cziter15/raesp_gateway/firmware/src/apps/raesp/comps/RadioCommander.cpp

/*
 *	Copyright (c) 2021-2023, Krzysztof Strehlau
 *
 *	This file is part of the RaespDevice (WiFi 433 MHz bridge) firmware.
 *	All licensing information can be found inside LICENSE.md file.
 *
 *	https://github.com/cziter15/raesp_gateway/blob/main/firmware/LICENSE
 */

#include "RadioCommander.h"
#include <RadioLib.h>

#include "board.h"
#include "../protocols/nexa.h"
#include "../protocols/ningbo.h"

using namespace std::placeholders;

namespace apps::raesp::comps
{
	RadioCommander::RadioCommander(uint8_t ssPin, uint8_t dio0pin, uint8_t rstPin, uint8_t dio2pin, ksLedWP& wifiLedWp, ksLedWP& radioLedWp)
		: radioLedWp(radioLedWp), wifiLedWp(wifiLedWp), rfTopicPrefix(PSTR("rfswitch/"))
	{
		/* Instantiate radio PHY/Module. */
		radioPhy = std::make_unique<Module>(ssPin, dio0pin, rstPin, dio2pin);
		radioModule = std::make_unique<SX1278>(radioPhy.get());

		/* Setup radio module. */
		cachedFrequency = TRANSMIT_FREQ_NEXA;
		radioModule->beginFSK(cachedFrequency, 4.8F, 5.0F, 125.0, TRANSMIT_POWER_DBM, 0, true);
		radioModule->setDirectSyncWord(0,0);

		/* Setup radio TX pin. */
		protocols::proto_prepare_txpin(dio2pin);
	}

	bool RadioCommander::postInit(ksf::ksApplication* app)
	{
		this->app = app;
		mqttConnWp = app->findComponent<ksf::comps::ksMqttConnector>();

		if (auto mqttConnSp{mqttConnWp.lock()})
		{
			mqttConnSp->onConnected->registerEvent(connEventHandleSp, std::bind(&RadioCommander::onMqttConnected, this));
			mqttConnSp->onDeviceMessage->registerEvent(msgEventHandleSp, std::bind(&RadioCommander::onMqttDevMessage, this, _1, _2));
		}

		return true;
	}

	void RadioCommander::onMqttConnected()
	{
		if (auto mqttConnSp{mqttConnWp.lock()})
			mqttConnSp->subscribe(rfTopicPrefix + '#');
	}

	void RadioCommander::onMqttDevMessage(const std::string_view& topic, const std::string_view& payload)
	{
		if (topic.find(rfTopicPrefix) == std::string_view::npos)
			return;

		/* Radio commander payload should be one char ('1' or '0') */
		if (payload.length() != 1)
			return;
			
		/* Check command queue overflow. */
		if (commandQueue.size() > MAX_TX_QUEUE_SIZE)
		{
			/* If overflow, then blink RED wifi LED. */
			if (auto wifiLedSp = wifiLedWp.lock())
				if (!wifiLedSp->isBlinking())
					wifiLedSp->setBlinking(100, 5);

			/* ... and send log about that. */
#if APP_LOG_ENABLED
			app->log([](std::string& out){
				out += PSTR("RadioCmd: Queue is full - discarding!");
			});
#endif
			return;
		}

		/*	
			Try split topic. Based of delimeter presence specific protocol is selected.

			Topics like OOK/1234/16 will be handled by nexa protocol.
			Topics like OOK/1 will be handled by ningbo protocol.
		*/
		uint32_t address{0};
		int16_t unit{RC_UNIT_NONE};
		
		if (auto delim_idx{topic.find('/', rfTopicPrefix.length() + 1)}; delim_idx != std::string_view::npos)
		{
			auto address_sv{topic.substr(rfTopicPrefix.length(), delim_idx - rfTopicPrefix.length())};
			if (!ksf::from_chars(address_sv, address))
				return;

			auto unit_sv{topic.substr(delim_idx + 1)};
			if (!ksf::from_chars(unit_sv, unit))
				return;
		}
		else
		{
			auto address_sv{topic.substr(rfTopicPrefix.length())};
			if (!ksf::from_chars(address_sv, address))
				return;
		}

		/* 
			If command queue is empty, the module is in IDLE state.
			We should set radio module to transmit mode and queue new request to send over air.
			Otherwise, we should have already transmit mode selected, so only queue in that case.
		*/
		if (commandQueue.empty())
		{
			GPOC = (1 << radioPhy->getGpio());
			radioModule->transmitDirect();
		}

		/* Push address/unit to command queue. */
		commandQueue.emplace(payload[0] == '1', address, unit, (uint8_t)(unit > 0 ? 6 : 9));
	}

	void RadioCommander::forceStandby()
	{
		/* Erase command queue. */
		commandQueue = {};

		/* Set radio module standby state - stop TX. */
		if (radioModule)
			radioModule->standby();
	}

	void RadioCommander::changeFrequency(double frequency)
	{
		if (cachedFrequency != frequency)
		{
			cachedFrequency = frequency;
			radioModule->setFrequency(frequency);
		}
	}

	void RadioCommander::processRadioCommand(RadioCommand &command)
	{
		int8_t ledPin{-1};

		if (auto radioLedSp{radioLedWp.lock()})
			ledPin = radioLedSp->getPin();
	
		/* Get radio pin and led pin. */
		uint8_t radioPin{static_cast<uint8_t>(radioPhy->getGpio())};

		/* Here we decide if we use ningbo protocol or nexa protocol. */
		if (command.unit == RC_UNIT_NONE)
		{
			changeFrequency(TRANSMIT_FREQ_NINGBO);
			protocols::tx_ningbo_switch({radioPin, ledPin}, command.enable, command.address);
		}
		else
		{
			changeFrequency(TRANSMIT_FREQ_NEXA);
			protocols::tx_nexa_switch({radioPin, ledPin}, command.enable, command.address, command.unit);
		}
		/* Decrement repeats countdown. */
		command.repeats--;
	}

	bool RadioCommander::loop(ksf::ksApplication* app)
	{
		if (!commandQueue.empty())
		{
			/*
				Handle single 'repeat' of OOK message request. 
				One request per application loop.
			*/
			auto& currentCommand{commandQueue.front()};
			processRadioCommand(currentCommand);
			
			/* Check if it's last repeat. */
			if (currentCommand.repeats <= 0)
			{
#if APP_LOG_ENABLED
				app->log([&](std::string& out){
					out += PSTR("RadioCmd: Sent! [ A: ");
					out += ksf::to_string(currentCommand.address);
					out += PSTR(" | U: ");
					out += ksf::to_string(currentCommand.unit);
					out += PSTR(" | V: ");
					out += ksf::to_string(currentCommand.enable);
					out += PSTR(" ]");
				});
#endif
				/* Pop current request (remove) from queue, coz we are done with it. */
				commandQueue.pop();
				
				/* If command queue is empty now, then call standby to get out of tx mode. */
				if (commandQueue.empty())
					radioModule->standby();
			}
		}

		return true;
	}

	RadioCommander::~RadioCommander() = default;
}
