cziter15/raesp_gateway/firmware/src/apps/raesp/comps/RadioCommander.h

/*
 *	Copyright (c) 2021-2023, Krzysztof Strehlau
 *
 *	This file is part of the RaespDevice (WiFi 433 MHz bridge) firmware.
 *	All licensing information can be found inside LICENSE.md file.
 *
 *	https://github.com/cziter15/raesp_gateway/blob/main/firmware/LICENSE
 */

#pragma once

#include <ksIotFrameworkLib.h>
#include <queue>

class Module;
class SX1278;

namespace apps::raesp::comps
{
	struct RadioCommand
	{
		bool enable;			// True to enable, false to disable.
		uint32_t address; 		// RF address.
		int16_t unit;			// RF unit.
		uint8_t repeats;		// Number of repeats.

		/*
			Constructor of RadioCommand.

			@param enable True to enable, false to disable.
			@param address RF address.
			@param unit RF unit.
			@param repeats Number of repeats.
		*/
		RadioCommand(bool enable, uint32_t address, int16_t unit, uint8_t repeats) :
			enable(enable), address(address), unit(unit), repeats(repeats) {}
	};

	class RadioCommander : public ksf::ksComponent
	{
		KSF_RTTI_DECLARATIONS(RadioCommander, ksf::ksComponent)
		
		using ksLedWP = std::weak_ptr<ksf::comps::ksLed>;

		protected:
			ksf::ksApplication* app{nullptr};													// Application ptr.

			static constexpr uint16_t MAX_TX_QUEUE_SIZE{20};									// Maximum queue size for RC requests.
			static constexpr int16_t RC_UNIT_NONE{-1};											// Value indicating no unit presence.

			std::unique_ptr<Module> radioPhy;													// Radio Phy module ptr.
			std::unique_ptr<SX1278> radioModule;												// Radio Module ptr.
			std::queue<RadioCommand> commandQueue;												// Radio commadn queue.

			std::weak_ptr<ksf::comps::ksMqttConnector> mqttConnWp;								// Weak pointer to mqtt connector.
			std::weak_ptr<ksf::comps::ksLed> radioLedWp, wifiLedWp;								// Weak pointers to LEDs.

			const std::string rfTopicPrefix;													// RF command topic prefix.
			std::unique_ptr<ksf::evt::ksEventHandle> connEventHandleSp, msgEventHandleSp;		// Shared ptrs to events.

			double cachedFrequency{0.0};														// Cached frequency value.

			/*
				Event handler method called when MQTT service receives a message.

				@param topic Topic reference (string_view).
				@param message Message (aka payload) reference (string_view).
			*/
			void onMqttDevMessage(const std::string_view& topic, const std::string_view& payload);

			/*
				Event handler method called when MQTT service connected to server. 
			*/
			void onMqttConnected();

			/*
				This funciton will handle one repeat of RadioCommand and will block to drive data pin.

				@param cmd Radio command reference.
			*/
			void IRAM_ATTR processRadioCommand(RadioCommand& cmd);

			/*
				Changes Radio Module frequency.

				@param freq Frequency to set.
			*/
			void IRAM_ATTR changeFrequency(double freq);
			
		public:
			/*
				Constructs RadioCommander.

				@param ssPin Radio Module SS pin number.
				@param dio0pin Radio Module DIO0 pin number.
				@param rstPin Radio Module reset pin number.
				@param dio2pin Radio Module DIO2 pin number.
				@param wifiLedWp Wifi LED component weak pointer.
				@param radioLedWp Radio LED component weak pointer.
			*/
			RadioCommander(uint8_t ssPin, uint8_t dio0pin, uint8_t rstPin, uint8_t dio2pin,	ksLedWP& wifiLedWp, ksLedWP& radioLedWp);

			/*
				Post initializes RadioCommander component.

				@param owner Pointer to owning ksApplication.
				@return True on success, false on fail.
			*/
			bool postInit(ksf::ksApplication* owner) override;

			/* 
				Handles RadioCommander logic.
				@param app Application object.
				@return True on success, false on fail.
			*/
			bool loop(ksf::ksApplication* app) override;

			/* 
				Stops all TX. Will clear radio command queue.
			*/
			void forceStandby();

			/*
				Destructor to free up resources.
			*/
			virtual ~RadioCommander();
	};
}
